krikun98/nijuni/pcb/nijuni.kicad_pcb

## KiCad design pcb/nijuni.kicad_pcb (2021-12-10)

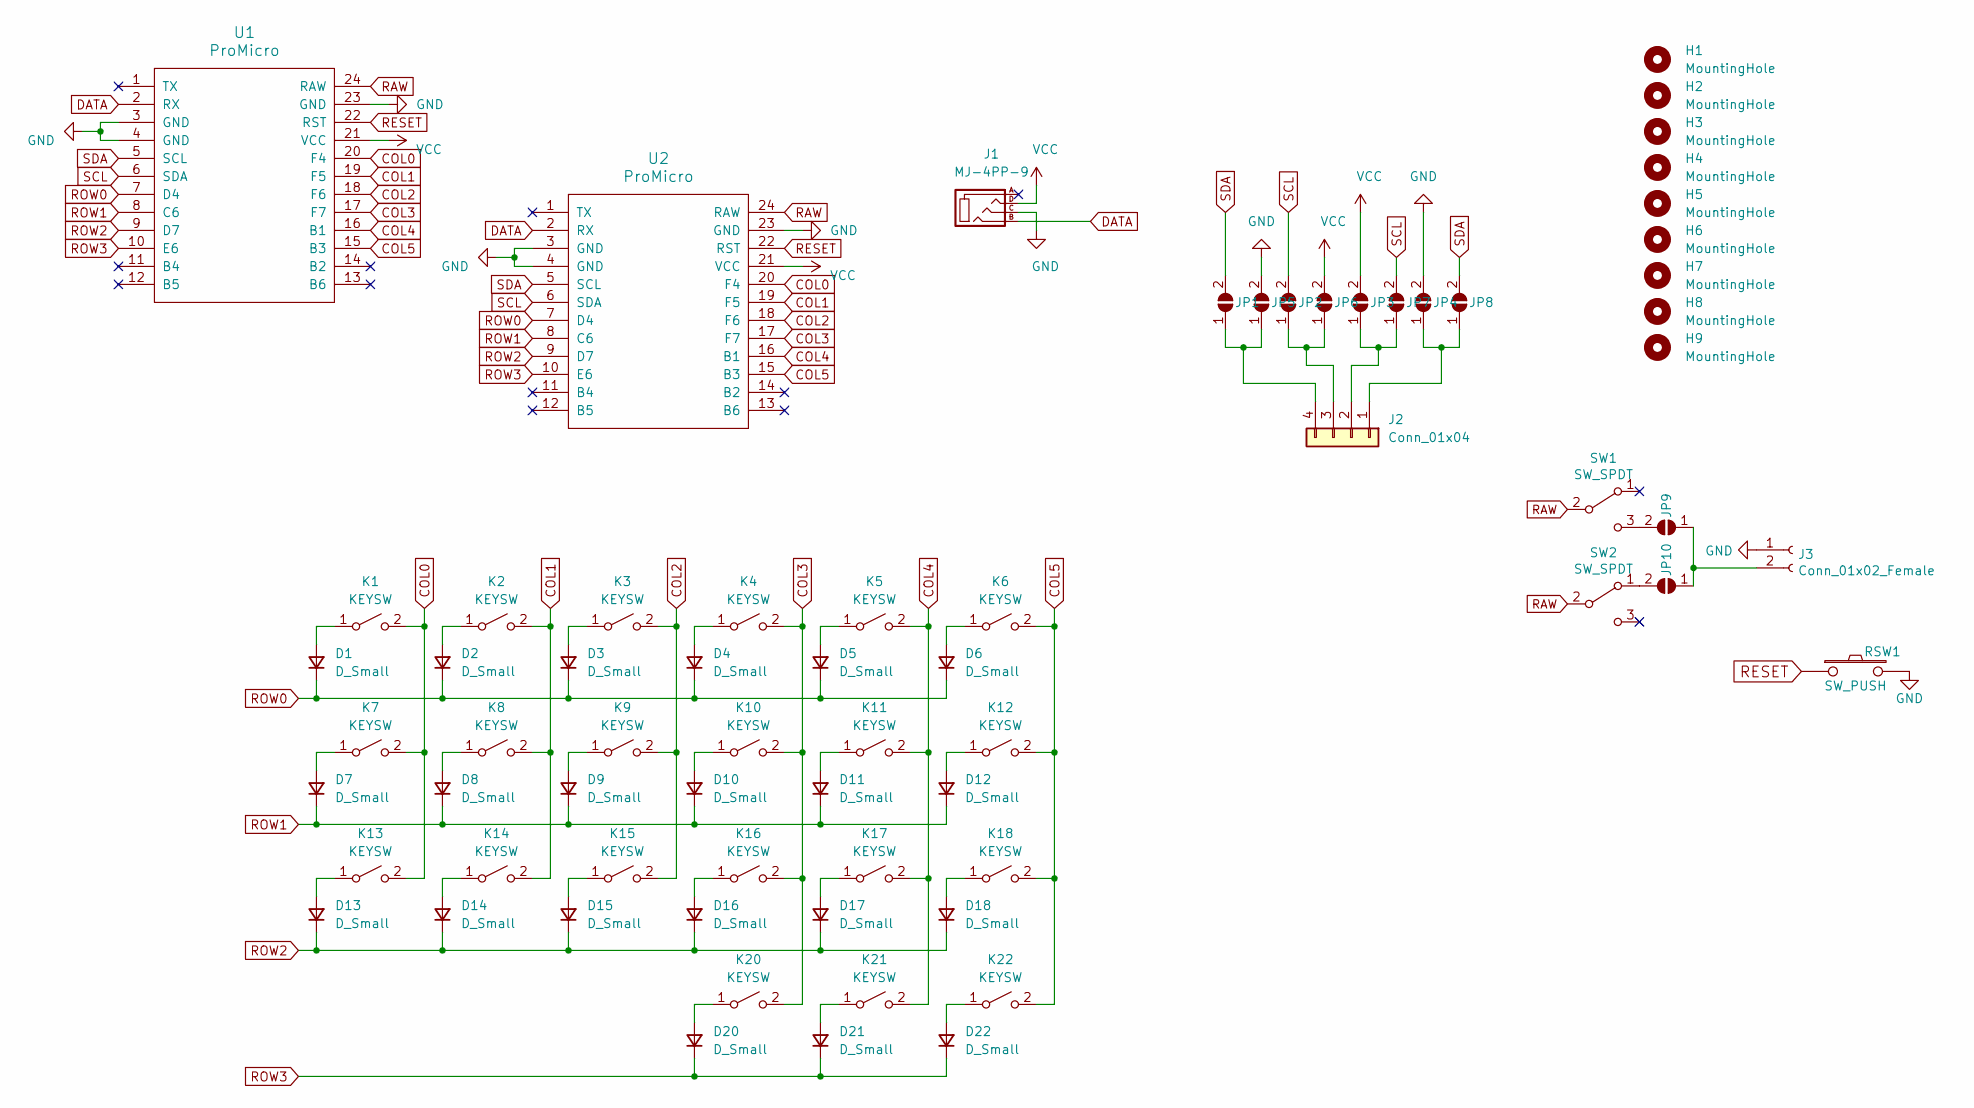
[picture p2: schematic nijuni.kicad_sch]

Parts:
D1, D2, D3, D4, D5, D6, D7, D8, D9, D10, D11, D12, D13, D14, D15, D16, D17, D18, D20, D21, D22: D_Small; D3_SMD
H1, H2, H3, H4, H5, H6, H7: MountingHole; M2-MountingHole-Standoff
H8, H9: MountingHole; M2-ClearanceHole
J1: MJ-4PP-9
J2: Conn_01x04; OLED_DISPLAY_128x32px_0.91in
J3: Conn_01x02_Female; Battery_TH
JP1, JP2, JP3, JP4, JP5, JP6, JP7, JP8, JP9, JP10: SolderJumper_2_Open; SolderJumper-2_P1.3mm_Open_RoundedPad1.0x1.5mm
K1, K2, K3, K4, K5, K6, K7, K8, K9, K10, K11, K12, K13, K14, K15, K16, K17, K18, K20, K21: KEYSW; MX-Alps-HS-1U-REV
K22: KEYSW; MX-Alps-HS-1.5U-REV
RSW1: SW_PUSH; ResetSW
SW1, SW2: SW_SPDT; SW_SPDT+H-MSK12C01_hor(7pin_SMD)
U1: ProMicro; ProMicro_Flipped_v2_A
U2: ProMicro; ProMicro_Flipped_v2_B

Connections:
COL0: K1.2 (B), K7.2 (B), K13.2 (B), U1.20 (F4), U2.20 (F4); also elsewhere on the board
COL1: K2.2 (B), K8.2 (B), K14.2 (B), U1.19 (F5), U2.19 (F5)
COL2: K3.2 (B), K9.2 (B), K15.2 (B), U1.18 (F6), U2.18 (F6)
COL3: K4.2 (B), K10.2 (B), K16.2 (B), K20.2 (B), U1.17 (F7), U2.17 (F7)
COL4: K5.2 (B), K11.2 (B), K17.2 (B), K21.2 (B), U1.16 (B1), U2.16 (B1)
COL5: K6.2 (B), K12.2 (B), K18.2 (B), K22.2 (B), U1.15 (B3), U2.15 (B3)
DATA: J1.B, U1.2 (RX), U2.2 (RX)
GND: J1.C, J3.1, JP4.2 (B), JP5.2 (B), RSW1.2, U1.3 (GND), U1.4 (GND), U1.23 (GND), U2.3 (GND), U2.4 (GND), U2.23 (GND)
unnamed: D1.2 (A), K1.1 (A)
unnamed: D2.2 (A), K2.1 (A)
unnamed: D3.2 (A), K3.1 (A)
unnamed: D4.2 (A), K4.1 (A)
unnamed: D5.2 (A), K5.1 (A)
unnamed: D6.2 (A), K6.1 (A)
unnamed: D7.2 (A), K7.1 (A)
unnamed: D8.2 (A), K8.1 (A)
unnamed: D9.2 (A), K9.1 (A)
unnamed: D10.2 (A), K10.1 (A)
unnamed: D11.2 (A), K11.1 (A)
unnamed: D12.2 (A), K12.1 (A)
unnamed: D13.2 (A), K13.1 (A)
unnamed: D14.2 (A), K14.1 (A)
unnamed: D15.2 (A), K15.1 (A)
unnamed: D16.2 (A), K16.1 (A)
unnamed: D17.2 (A), K17.1 (A)
unnamed: D18.2 (A), K18.1 (A)
unnamed: D20.2 (A), K20.1 (A)
unnamed: D21.2 (A), K21.1 (A)
unnamed: D22.2 (A), K22.1 (A)
unnamed: J2.1, JP4.1 (A), JP8.1 (A)
unnamed: J2.2, JP3.1 (A), JP7.1 (A)
unnamed: J2.3, JP2.1 (A), JP6.1 (A)
unnamed: J2.4, JP1.1 (A), JP5.1 (A)
unnamed: J3.2, JP9.1 (A), JP10.1 (A)
unnamed: JP9.2 (B), SW1.3 (C)
unnamed: JP10.2 (B), SW2.1 (A)
RAW: SW1.2 (B), SW2.2 (B), U1.24 (RAW), U2.24 (RAW)
RESET: RSW1.1, U1.22 (RST), U2.22 (RST)
ROW0: D1.1 (K), D2.1 (K), D3.1 (K), D4.1 (K), D5.1 (K), D6.1 (K), U1.7 (D4), U2.7 (D4)
ROW1: D7.1 (K), D8.1 (K), D9.1 (K), D10.1 (K), D11.1 (K), D12.1 (K), U1.8 (C6), U2.8 (C6)
ROW2: D13.1 (K), D14.1 (K), D15.1 (K), D16.1 (K), D17.1 (K), D18.1 (K), U1.9 (D7), U2.9 (D7)
ROW3: D20.1 (K), D21.1 (K), D22.1 (K), U1.10 (E6), U2.10 (E6); also elsewhere on the board
SCL: JP2.2 (B), JP7.2 (B), U1.6 (SDA), U2.6 (SDA)
SDA: JP1.2 (B), JP8.2 (B), U1.5 (SCL), U2.5 (SCL)
VCC: J1.D, JP3.2 (B), JP6.2 (B), U1.21 (VCC), U2.21 (VCC)

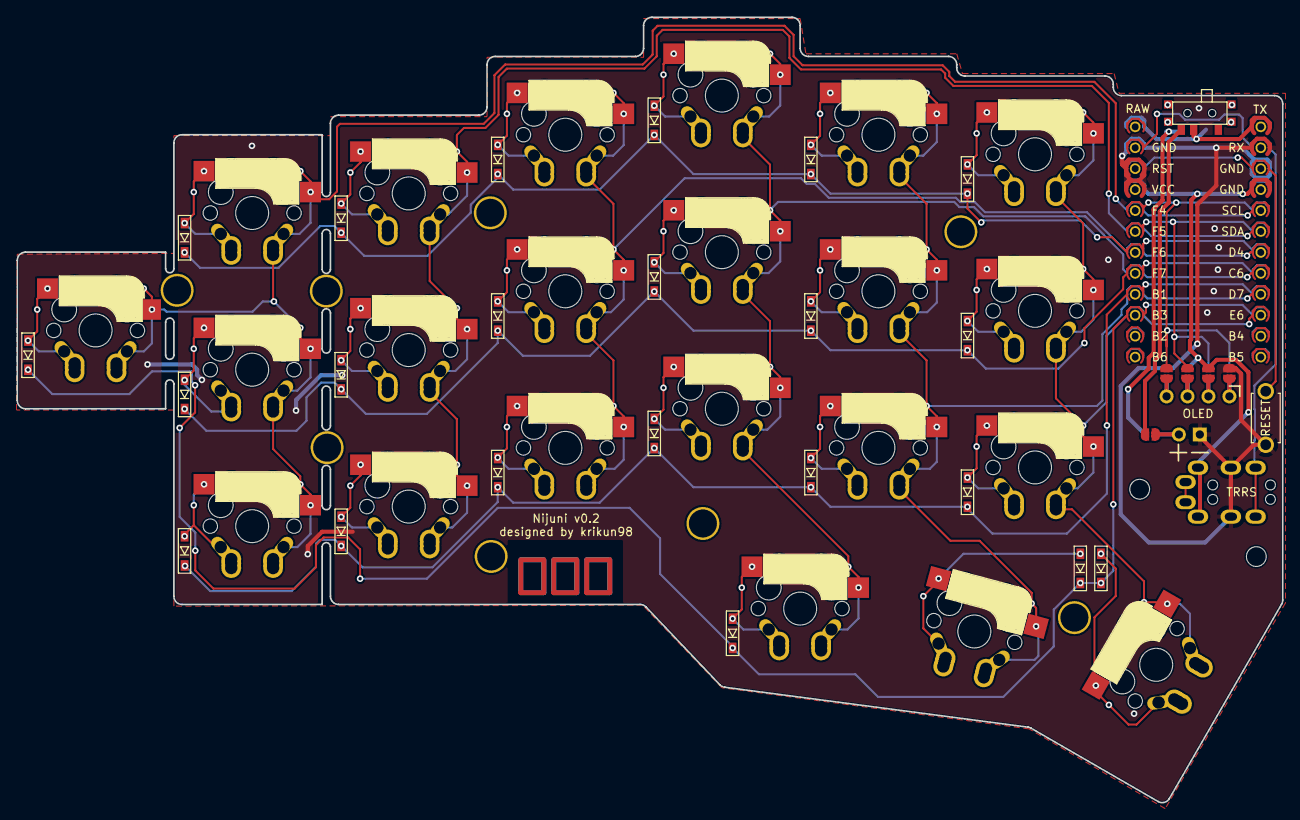
[picture p3: board nijuni.kicad_pcb from above]

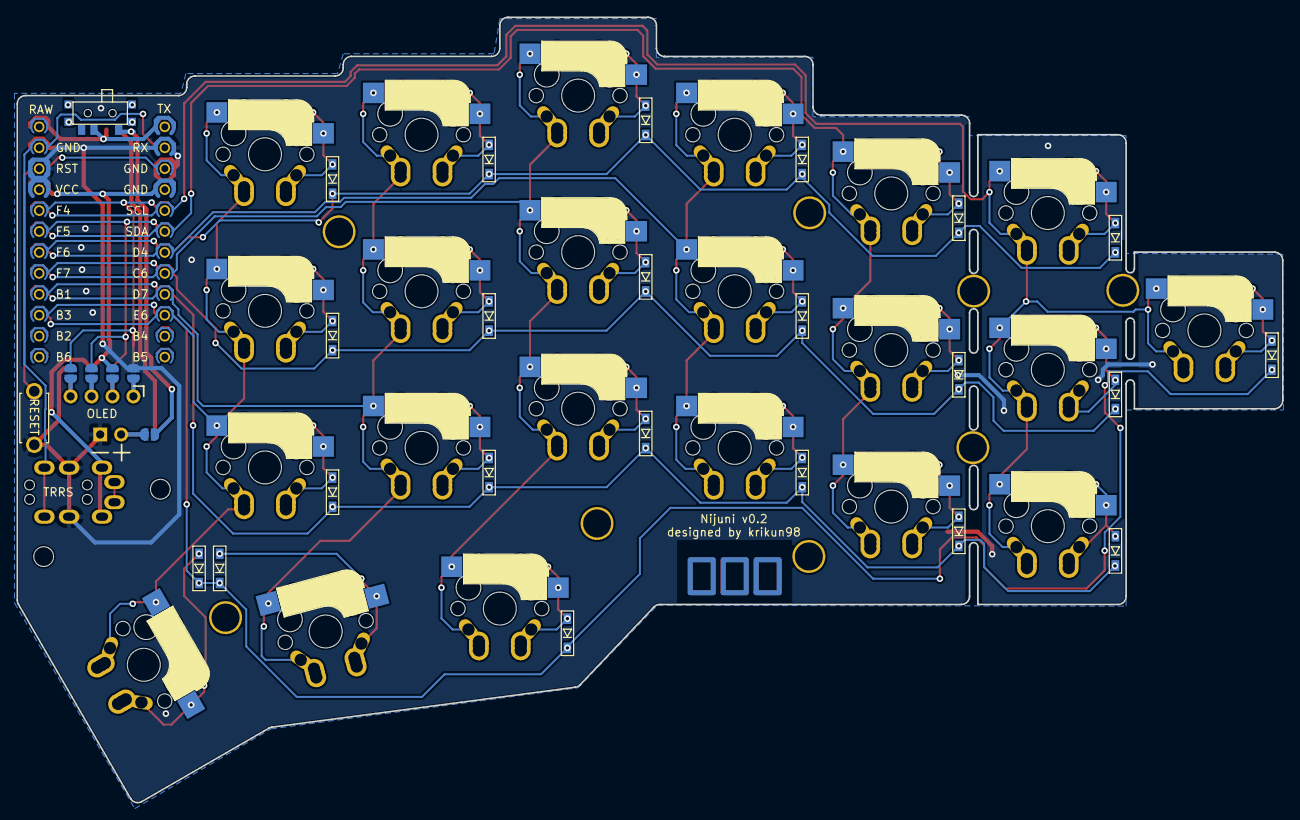
[picture p4: board nijuni.kicad_pcb from below]

Board: 2 copper layers, 153.6 x 95.3 mm, 72 parts (7 on the bottom side), 46 nets.

Other parts of the board:
D19: D_Small; D3_SMD
H0: MountingHole; M2-MountingHole-Standoff
K19: KEYSW; MX-Alps-HS-1U-REV

Their connections:
COL0: K19.2 (B); also elsewhere on the board
unnamed: D19.2 (A), K19.1 (A)
ROW3: D19.1 (K); also elsewhere on the board
